roge-rm/hans/images/withfriend.jpg

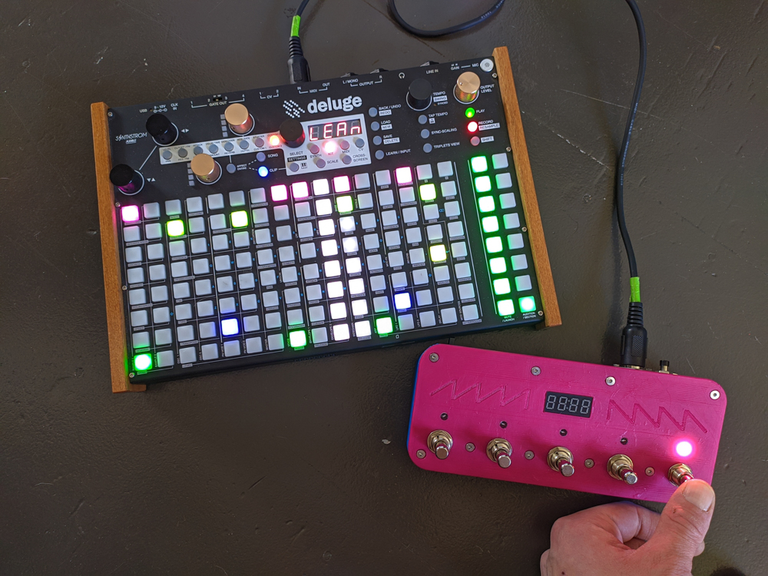
images/withfriend.jpg
