roge-rm/hans/builds/002/002-inside.jpg

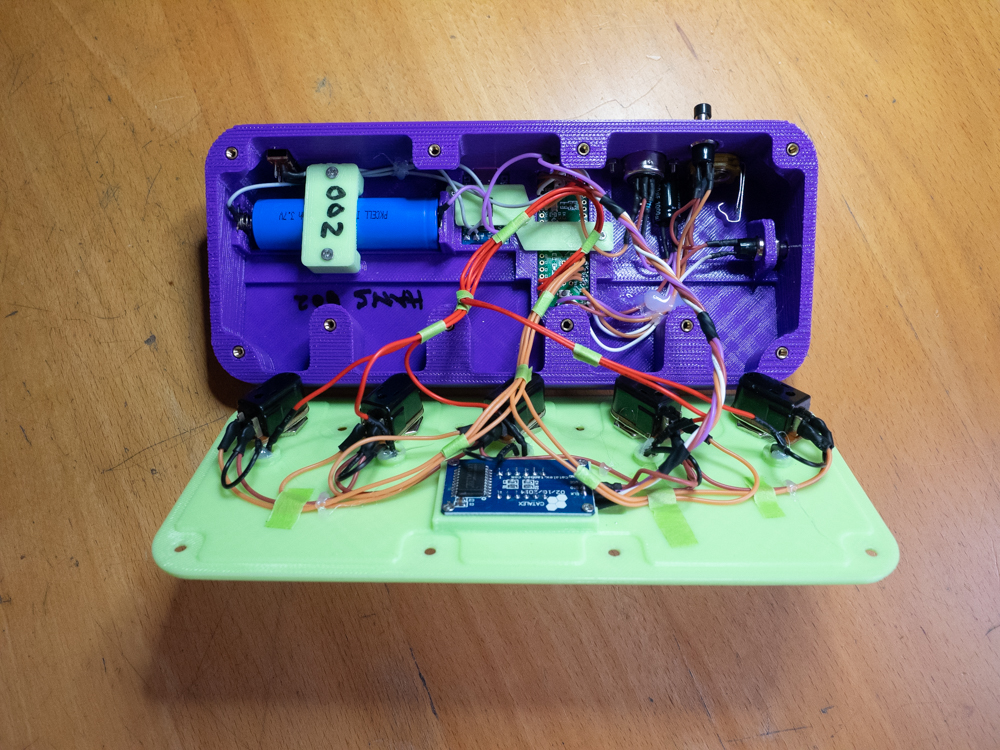
builds/002/002-inside.jpg
