roge-rm/hans/builds/002/002-top.jpg

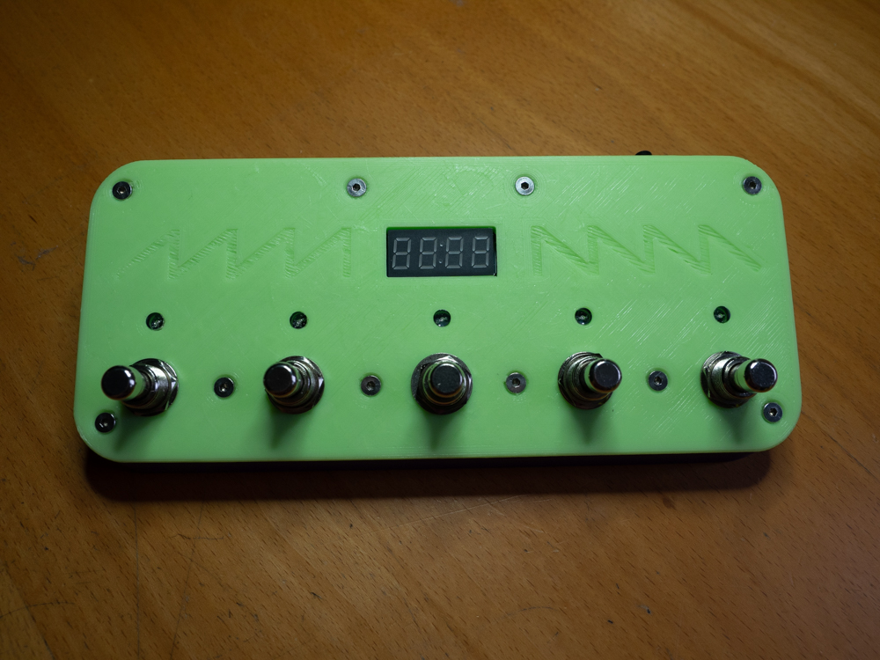
builds/002/002-top.jpg
